sgreg/4chord-midi/firmware/gui.c

/*
 * 4chord MIDI - LCD graphical user interface
 *
 * Copyright (C) 2018 Sven Gregori <sven@craplab.fi>
 *
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
 */
#include <stdint.h>
#include "gfx.h"
#include "lcd.h"
#include "menu.h"

/* graphics data array for menus */
static const unsigned char *menus[] = {
    gfx_menu_key,
    gfx_menu_mode,
    gfx_menu_tempo,
    gfx_menu_metre
};

/* graphics data array for tempo digits */
static const unsigned char *tempo_digits[] = {
    gfx_tempo_0,
    gfx_tempo_1,
    gfx_tempo_2,
    gfx_tempo_3,
    gfx_tempo_4,
    gfx_tempo_5,
    gfx_tempo_6,
    gfx_tempo_7,
    gfx_tempo_8,
    gfx_tempo_9,
};

/* graphics data array for modes */
static const unsigned char *modes[] = {
    gfx_mode_chord,
    gfx_mode_chord_arp,
    gfx_mode_chord_arp_oct,
    gfx_mode_arp,
    gfx_mode_arp_oct
};

/* graphics data array for key chords and modifiers */
static const unsigned char *chords[][2] = {
    {gfx_key_c, gfx_key_none},
    {gfx_key_c, gfx_key_sharp},
    {gfx_key_d, gfx_key_none},
    {gfx_key_d, gfx_key_sharp},
    {gfx_key_e, gfx_key_none},
    {gfx_key_f, gfx_key_none},
    {gfx_key_f, gfx_key_sharp},
    {gfx_key_g, gfx_key_none},
    {gfx_key_g, gfx_key_sharp},
    {gfx_key_a, gfx_key_none},
    {gfx_key_b, gfx_key_flat},
    {gfx_key_b, gfx_key_none},
};

/**
 * Display the given menu item graphic on the LCD.
 * @param Menu item index in accordance with menu.h values
 */
void
gui_set_menu(menu_item_t item)
{
    lcd_set_menu(menus[item]);
}

/**
 * Display the given playback mode item graphic on the LCD.
 * @param Playback mode item index in accordance with menu.h values
 */
void
gui_set_playback_mode(playback_mode_item_t item)
{
    lcd_set_mode(modes[item]);
}

/**
 * Display the given playback key item graphic on the LCD.
 * @param Playback key item index in accordance with menu.h values
 */
void
gui_set_playback_key(playback_mode_item_t item)
{
    lcd_set_chord(chords[item]);
}

/**
 * Display the given tempo value on the LCD.
 * Takes tempo as 8 bit integer (>255bpm won't be supported anyway) and
 * splits it in three single digits. The digits' representing graphics
 * are then transferred to the LCD's tempo area.
 *
 * @param tempo New tempo
 */
void
gui_set_playback_tempo(uint8_t tempo)
{
    const unsigned char *digit_graphics[3];
    uint8_t digits[3];
    uint8_t one, ten, hundred;

    /* split integer to three digits */
    one = tempo / 10;
    digits[2] = tempo - (one * 10);
    ten = one / 10;
    digits[1] = one - (ten * 10);
    hundred = ten / 10;
    digits[0] = ten - (hundred * 10);

    digit_graphics[0] = (digits[0] == 0) ? gfx_tempo_none : tempo_digits[digits[0]];
    digit_graphics[1] = tempo_digits[digits[1]];
    digit_graphics[2] = tempo_digits[digits[2]];

    lcd_set_tempo(digit_graphics);
}

/**
 * Display the given metre value on the LCD.
 * @param Menu item index in accordance with menu.h values
 */
void
gui_set_playback_metre(playback_metre_item_t metre)
{
    /* there may be a better way for this.. but not today. Hard coded it is */
    switch (metre) {
        case PLAYBACK_METRE_4_4:
            lcd_set_metre(4, 4);
            break;
        case PLAYBACK_METRE_3_4:
            lcd_set_metre(3, 4);
            break;
        case PLAYBACK_METRE_6_8:
            lcd_set_metre(6, 8);
            break;
        default:
            break;
    }
}
